josamuna/codepo-electronic-2021/firmware/adc.h

/* 
 * File:   adc.h
 * Author: mosee
 */

#ifndef ADC_H
#define	ADC_H

/**
 * En-tÍte de la librairie de l'ADC pour ELEC-H309
 * 
 * Ces fonctions utilisent l'ADC1 du dsPIC pour convertir le signal de AN0.
 * 
 * L'ADC peut Ítre utilisÈ dans 2 modes, par adcInit() :
 *   - en "manuel" : les conversions sont dÈmarrÈes en appelant adcStart(). 
 *     C'est donc la boucle principale qui rythme l'Èchantillonnage
 *   - dÈclenchÈ par le timer3 : dans ce mode, une conversion est dÈmarrÈe 
 *     ? chaque dÈbordement du timer3. La frÈquence d'Èchantillonnage est alors
 *     dÈfinie par PR3.
 * Comme une conversion prend plusieurs cycles d'horloge, il faut utiliser 
 * adcConversionDone() pour "poller" la fin d'une conversion.
 * L'Èchantillon peut alors Ítre lu avec adcRead().
 */


#define ADC_MANUAL_SAMPLING 0
#define ADC_TIMER3_SAMPLING 2

/**
 * Initialise l'ADC1 pour convertir AN0, sur 10 bits
 * ParamËtre:
 *  - mode : dÈfinit le mode de fonctionnement. Il peut prendre 2 valeurs :
 *     - ADC_MANUAL_SAMPLING : les conversions sont lancÈes par adcStart()
 *     - ADC_TIMER3_SAMPLING : la frÈquence d'Èchantillonnage est dÈfinie
 *          par le TIMER3. NE PAS UTILISER adcStart() DANS CE MODE !
 */
void adcInit(int mode);


/**
 * DÈmarre une conversion. A n'utiliser qu'en mode ADC_MANUAL_SAMPLING
 */
void adcStart(int pin);

/**
 * renvoie 1 si la conversion est terminÈe, 0 sinon
 */
int adcConversionDone(void);

/**
 * Renvoie le rÈsultat de la derniËre conversion.
 * Si on essaie de lire pendant une conversion, la fonction le dÈtecte et 
 * renvoie -32768, qui est une valeur impossible comme rÈsultat de conversion.
 */
int adcRead(void);


#endif	/* ADC_H */
